VaAndCob/ESP32-OBD2-Gauge/hardware/12-5v micro usb.jpg

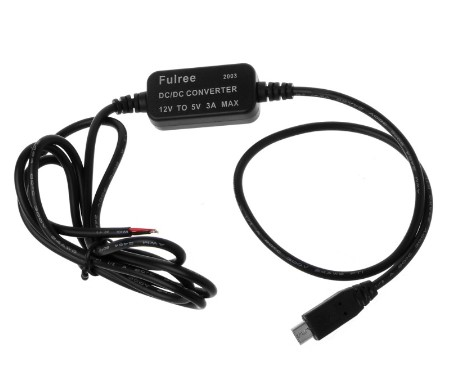
hardware/12-5v micro usb.jpg
