VaAndCob/ESP32-OBD2-Gauge/hardware/ELM327_bluetooth.png

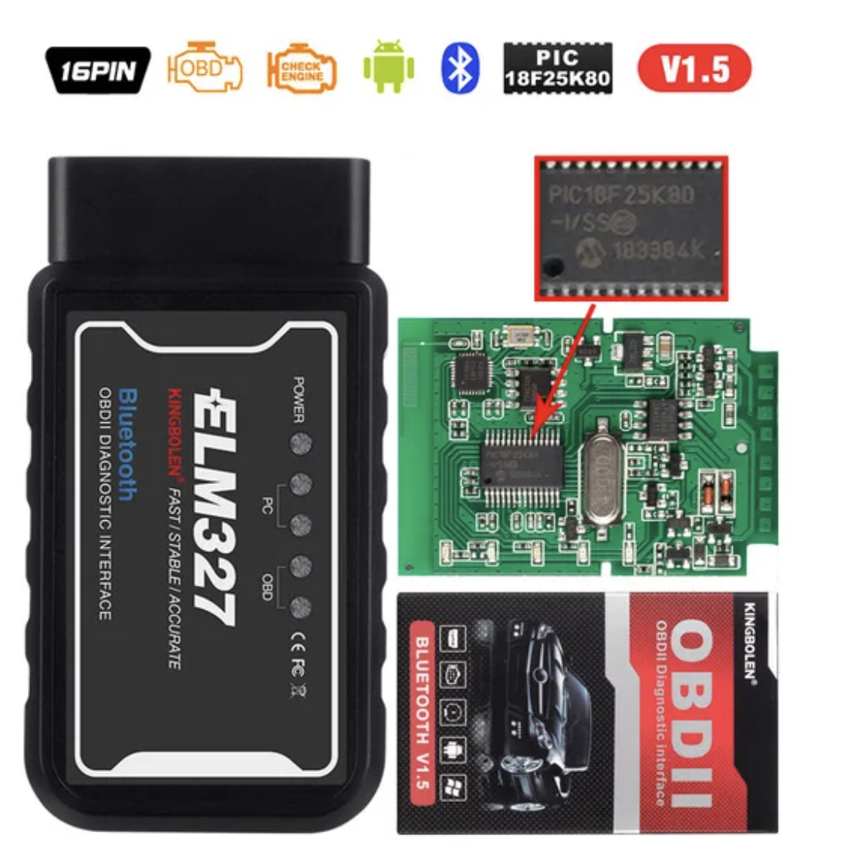
hardware/ELM327_bluetooth.png
