VaAndCob/ESP32-OBD2-Gauge/hardware/ESP32-2432S028-LCM001.jpeg

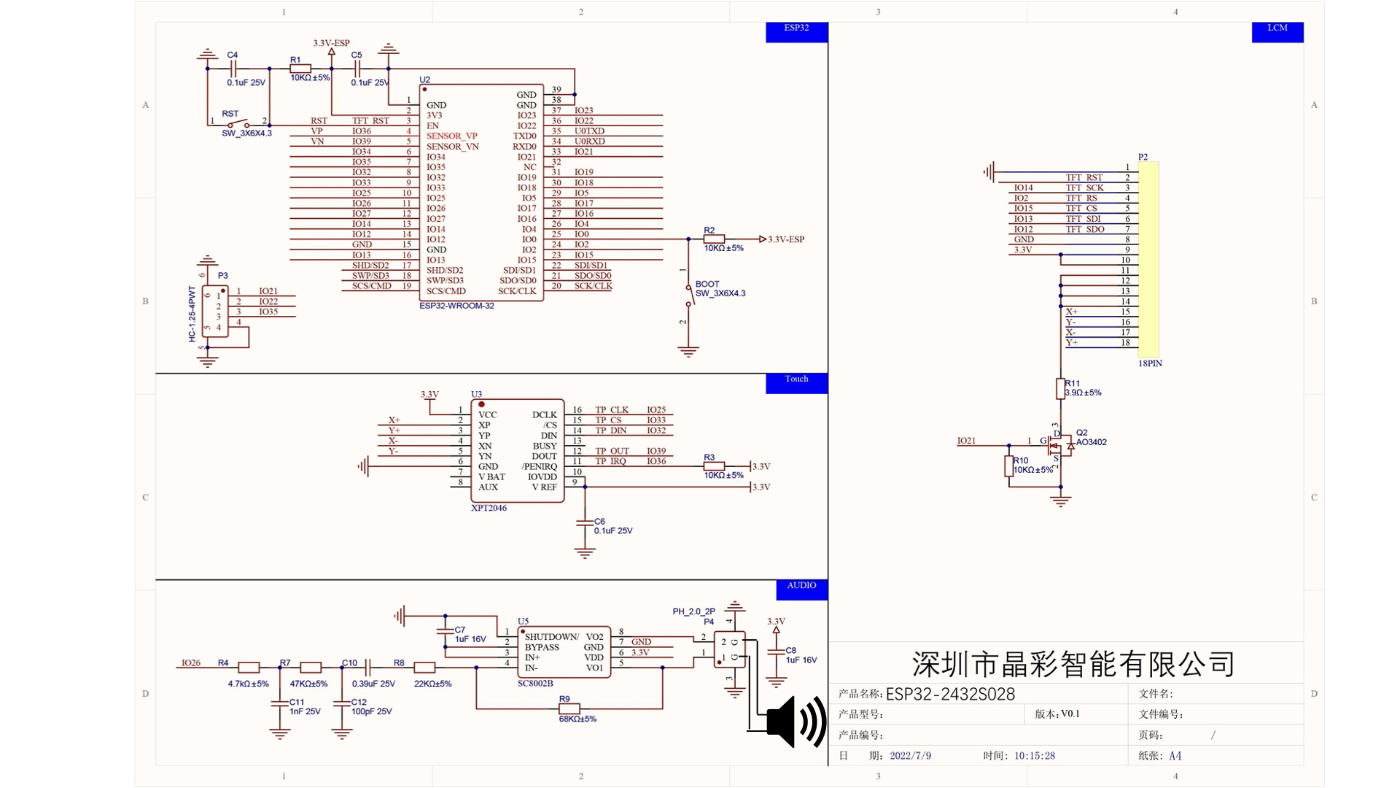
hardware/ESP32-2432S028-LCM001.jpeg
