VaAndCob/ESP32-OBD2-Gauge/picture/cover.jpg

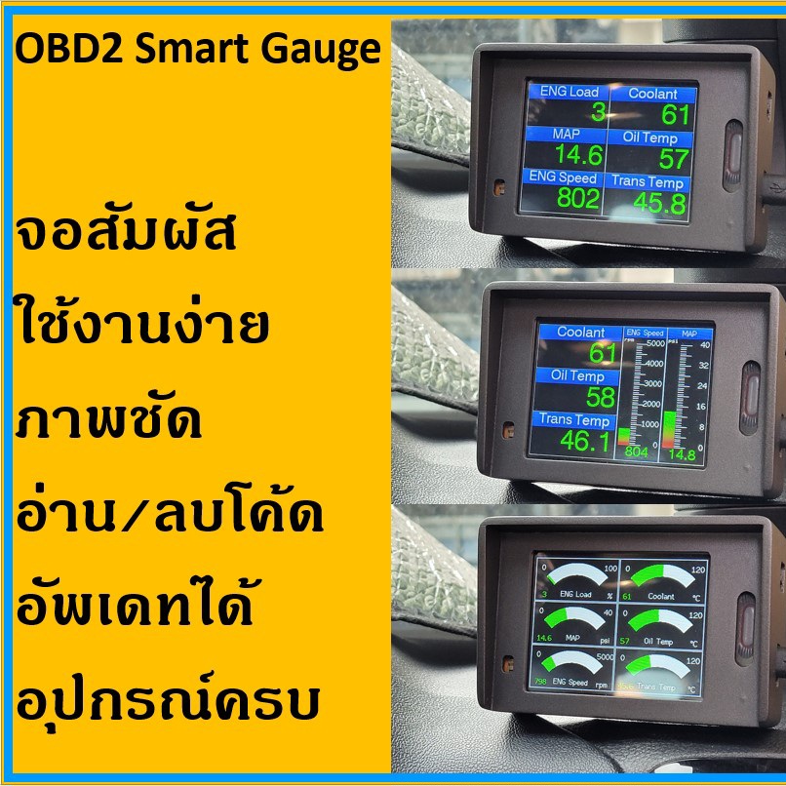
picture/cover.jpg
