VaAndCob/ESP32-OBD2-Gauge/picture/fullpart.jpg

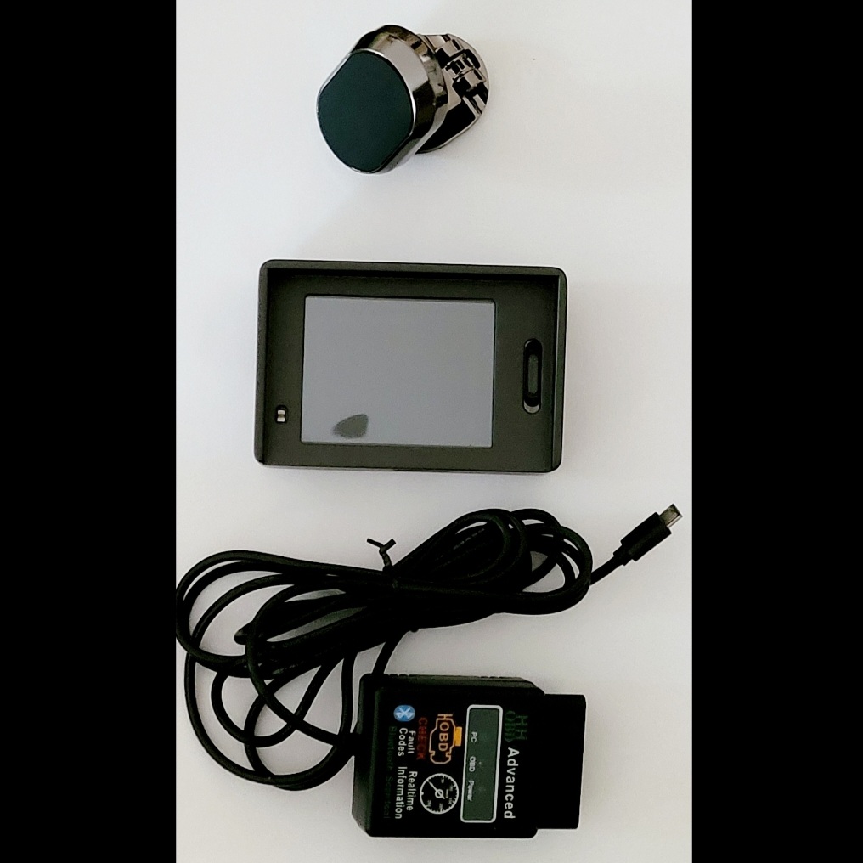
picture/fullpart.jpg
