VaAndCob/ESP32-OBD2-Gauge/picture/gauge.jpg

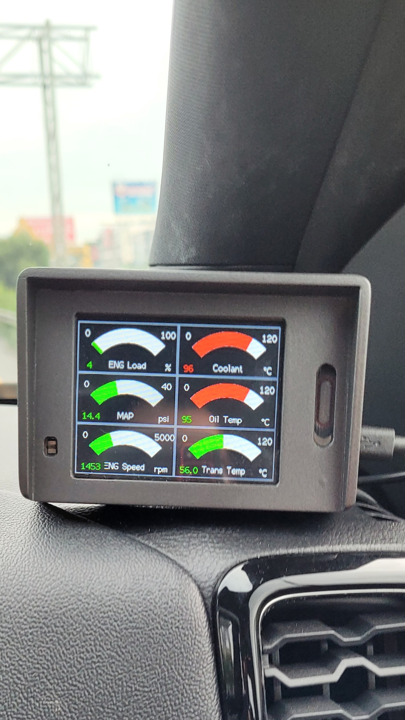
picture/gauge.jpg
