VaAndCob/ESP32-OBD2-Gauge/SDCard/mypic.jpg

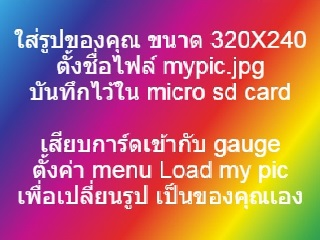
SDCard/mypic.jpg
