VaAndCob/ESP32-OBD2-Gauge/sketch/VaAndCobOBD2Gauge/firmware/offset.png

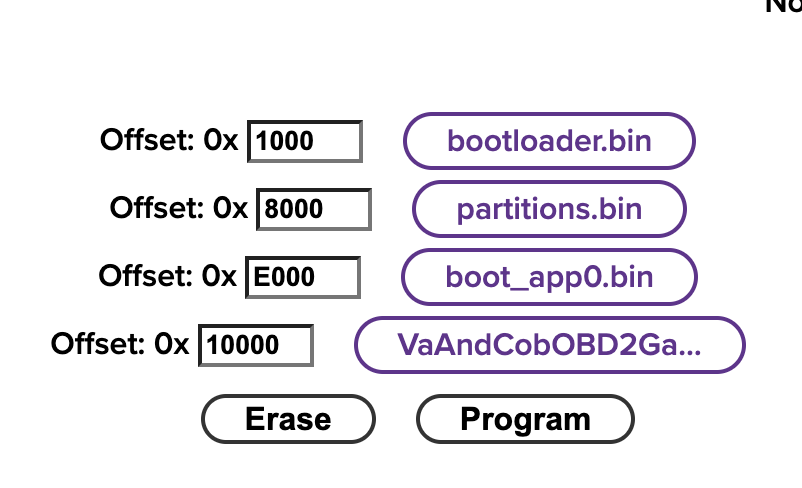
sketch/VaAndCobOBD2Gauge/firmware/offset.png
