VaAndCob/ESP32-OBD2-Gauge/sketch/arduinoSetup.png

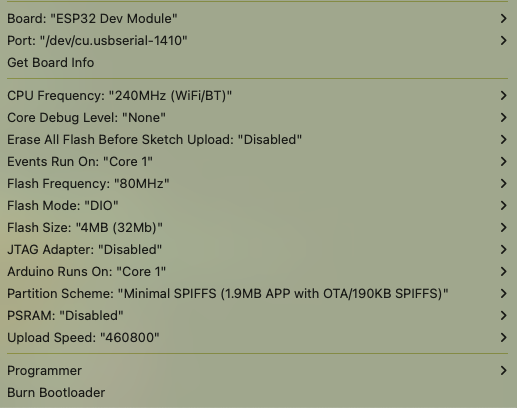
sketch/arduinoSetup.png
