VaAndCob/ESP32-OBD2-Gauge/sketch/VaAndCobOBD2Gauge/firmware_update.h

//Firmware updater library
#include <esp_ota_ops.h>//ota partition boot option
#include <Update.h>  // main updater
#include <FS.h>      // File System
#include <SD.h>      // SD Card ESP32
#include <SPIFFS.h>  //safe file

//Wifi updater
#include <WiFi.h>   //wifi
#include <WebServer.h>

const char* ssid = "Va&Cob OBD2 Gauge";
const char* password = "12345678";//default password
IPAddress local_IP(192, 168, 4,1);
IPAddress gateway(192, 168, 4, 1);
IPAddress subnet(255, 255, 255, 0);
WebServer server(80);

#define firmware_filename "/VaAndCobOBD2Gauge.bin"//firmware file 


/*------------ SOUND EFFECT ----------*/
 void beepbeep() { //2 shot beep
  ledcWriteTone(buzzerChannel,2000);
  delay(50);
  ledcWriteTone(buzzerChannel,0);
  delay(50);
  ledcWriteTone(buzzerChannel,2000);
  delay(50);
  ledcWriteTone(buzzerChannel,0);
 }              
 void beep() { 
  ledcWriteTone(buzzerChannel,2000);
  delay(500);
  ledcWriteTone(buzzerChannel,0);
 }  
 void clickSound() {
  ledcWriteTone(buzzerChannel,5000);
  delay(5);
  ledcWriteTone(buzzerChannel,0);
 } 
 /*-----------------------------*/
//html update file
static const char uploadIndex[] PROGMEM =
R"(
<!DOCTYPE html>
<head>
<meta name='viewport' content='width=device-width'/>
</head>
<body>
<img src="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"width="100%">
<h3 style='color:blue;'>Please choose file 'vaandcobobd2gauge.bin'</h3>
<form method='POST' action='#' enctype='multipart/form-data' id='upload_form'>
<input type='file' name='update' accept=".bin" id='file1' onchange='uploadFile()'>
</form>
<p style='align:center'>
<progress id='progressBar' value='0' max='100' style='width:100%'></progress>
<div id='status' style='text-align:center';>0%</div>
</p>
<script>
function _(el) {
  return document.getElementById(el);
}
function uploadFile() {
  let file = _('file1').files[0];
  // alert(file.name+' | '+file.size+' | '+file.type);
  let req = new XMLHttpRequest();
  let formdata = new FormData();
  formdata.append('file1', file);
   req.upload.addEventListener('progress', progressHandler, false);
  req.addEventListener('load', completeHandler, false);
  req.addEventListener('error', errorHandler, false);
  req.addEventListener('abort', abortHandler, false);
  req.open('POST', '/update'); 
  req.send(formdata);
}
function progressHandler(event) {
  var percent = (event.loaded / event.total) * 100;
  _('progressBar').value = Math.round(percent);
  _('status').innerHTML = Math.round(percent) + '%';
}
function completeHandler(event) {
  _('status').innerHTML = 'Restarting...';
}
function errorHandler(event) {
  _('status').innerHTML = 'Upload Failed';
}
function abortHandler(event) {
  _('status').innerHTML = 'Upload Aborted';
}
</script>
</body>
</html>
)";
/*----- OTA Web Server ------*/
void  StartOTAserver() {
  //open upload page  http://192.168.4.1
  server.on("/", HTTP_GET, []() {
    Serial.println(F("Request upload firmware..."));
    server.sendHeader("Connection", "close");
    server.send(200, "text/html", uploadIndex);
  });

  //handling uploading firmware file http://192.168.4.1/update
  server.on("/update", HTTP_POST, []() {
    server.sendHeader("Connection", "close");
    server.send(200, "text/plain", (Update.hasError()) ? "FAIL" : "OK");
    if (Update.hasError()) {//error 
      tft.setTextColor(TFT_WHITE,TFT_RED);
      tft.drawCentreString("Error: bad firmware file!",159,170,4); 
      beep();
    } 
    else {
      esp_ota_mark_app_valid_cancel_rollback();//prevent from boot old firmware
      delay(3000);
      ESP.restart();//successful upload restart esp
    }  
  }, []() {
    
    HTTPUpload& upload = server.upload();
    if (upload.status == UPLOAD_FILE_START) {
      beepbeep();
      Serial.printf("Firmware: %s\n", upload.filename.c_str());
      tft.setTextColor(TFT_BLACK,TFT_GREEN);
      tft.drawCentreString("Updating... please wait",159,170,4); 
      if (!Update.begin(UPDATE_SIZE_UNKNOWN)) { //start with max available size
        Update.printError(Serial);        
      }
    } else if (upload.status == UPLOAD_FILE_WRITE) {
      // flashing firmware to ESP
      if (Update.write(upload.buf, upload.currentSize) != upload.currentSize) {
        Update.printError(Serial);
      }
    } else if (upload.status == UPLOAD_FILE_END) {
      if (Update.end(true)) { //true to set the size to the current progress
        Serial.printf("Update Successful... Restart");
        tft.setTextColor(TFT_BLACK,TFT_GREEN);
        tft.drawCentreString("Update Successful... Restart",159,170,4); 
        beepbeep();

      } else {
        Update.printError(Serial);  
      }
    }
  });
  server.begin();
}//startOTAserver
/*-------------- WiFi Updater----------------*/
void updateFirmwareWIFI() {  
  WiFi.mode(WIFI_AP);//set wifi mode soft access point
  String pwd = String(random(99999999));//random new password at least 8 digit long to get it work
  for (uint8_t i=pwd.length();i<8;i++) {
    pwd = "0"+pwd;//add 0 prefix to set 8 char length password
  }
  password = pwd.c_str();
  WiFi.softAP(ssid, password);//start ACCESS Point
  if (!WiFi.softAPConfig(local_IP, gateway, subnet)) {//error start soft AP
    Serial.println(F("STA Failed to configure"));
    tft.setTextColor(TFT_WHITE,TFT_RED);
    tft.drawCentreString("Failed to start WiFi!",159,120,4); 
    beep();
    delay(3000); 
  } else {//softAP config OK
    StartOTAserver();//start server
  //show WiFi softAP information
    tft.fillRect(0,30,320,239,TFT_BLACK);
    tft.setTextColor(TFT_CYAN,TFT_BLACK);
    tft.drawCentreString("> Connect to gauge Wi-Fi <",159,40,4); 
    tft.setTextColor(TFT_WHITE,TFT_BLACK); 
    String txt = "SSID: "+String(ssid);
    Serial.println(txt);
    tft.drawString(txt,0,80,4);
    txt = "Password: "+String(password);
    Serial.println(txt);
    tft.drawString(txt,0,110,4);
    txt = "IP Address: "+ WiFi.softAPIP().toString();
    Serial.println(txt);
    tft.drawString(txt,0,140,4);  
    tft.setTextColor(TFT_BLACK,TFT_WHITE);
    tft.drawCentreString("[- Press button to exit -]",159,215,4);  
    while (digitalRead(SELECTOR_PIN) == HIGH) {//wait for button press to exit       
      autoDim();
      checkCPUTemp(); 
      server.handleClient();//update server handle      
      delay(300);//delay button press
    } //exit wifi update      
    clickSound();   
    server.stop();
    WiFi.mode(WIFI_MODE_STA);
    WiFi.softAPdisconnect();//turn off WiFi
  }//else WiFi.softapconfig
} //updateFirmwareWiFI
/*----------- SD Card Updater --------------*/
// perform the actual update from a given stream
void performUpdate(Stream &updateSource, size_t updateSize) {
  if (Update.begin(updateSize, U_FLASH, LED_RED_PIN, LOW)) { 
      //add progressbar
      tft.fillRoundRect(50,61, 218, 28, 14, TFT_LIGHTGREY);
      tft.fillRect(59,67,200,16,TFT_BLACK);//0% progress bar
      //update progress
      Serial.print(F("Progress: "));
      //progress callback
     Update.onProgress([&](size_t written, size_t total) {
      uint8_t progress = written * 100 / total;
      tft.fillRectHGradient(59,67,progress*2,16,TFT_RED,TFT_GREEN);//progressbar 
      if (progress%10 == 0) Serial.print(F("*"));
      ledcWriteTone(buzzerChannel,random(4000)+8000);//acceleraet sound effect
    }); 

    //write firmware from SDCard here
      size_t written = Update.writeStream(updateSource);
      Serial.printf("%d bytes written",written);

     if (Update.end()) {//updaet is done
         if (Update.isFinished()) {
            Serial.println(F("Update Successful... Restart"));
            tft.setTextColor(TFT_BLACK,TFT_GREEN);
            tft.drawCentreString("Update Successful... Restart",159,120,4);  
            beepbeep();
            esp_ota_mark_app_valid_cancel_rollback();//prevent from boot old firmware
            delay(1000);
            ESP.restart();//restart
         }
         else {
            Serial.println(F("Error! Update not finished"));
            tft.setTextColor(TFT_WHITE,TFT_RED);
            tft.drawCentreString("Error! Update not finished",159,120,4); 
         }
      } else {//update stop during updating
         Serial.println("Error Occurred. Error #: " + String(Update.getError()));
      }

   }//if update.begin
   else
   {
      Serial.println(F("Not enough space to load firmware"));
      tft.setTextColor(TFT_WHITE,TFT_RED);
      tft.drawCentreString("Not enough space to upload!",159,120,4); 
   }
}
/*------------------*/
// check given FS for valid update.bin and perform update if available
void updateFromFS(fs::FS &fs) {
   Serial.println(F("Loading firmware..."));
   tft.setTextColor(TFT_WHITE,TFT_BLUE);
   tft.drawCentreString("Loading firmware...",159,120,4);
   File updateBin = fs.open(firmware_filename);
   if (updateBin) {
 
      if(updateBin.isDirectory()){
         Serial.println(F("\"VaandCobOBD2Gauge.bin\" is not a file"));
         tft.setTextColor(TFT_WHITE,TFT_RED);
         tft.drawCentreString("\"VaandCobOBD2Gauge.bin\" is not a file",159,120,4);
         updateBin.close();
         return;
      }
    
      size_t updateSize = updateBin.size();

      if (updateSize > 0) {
         Serial.println(F("Updating... please wait"));
         tft.setTextColor(TFT_WHITE,TFT_BLUE);
         tft.drawCentreString("Updating... please wait",159,120,4);
         performUpdate(updateBin, updateSize);
      }
      else {
         Serial.println(F("Error! file is empty"));
         tft.setTextColor(TFT_WHITE,TFT_RED);
         tft.drawCentreString("Error! file is empty",159,120,4);               
      }
      updateBin.close();
      // whe finished remove the binary from sd card to indicate end of the process
      //fs.remove(firmware_filename);  
   
   } else {
      Serial.println(F("Firmware not found!"));
      tft.pushImage(130,44,60,60,nofile);//show fileicon
      tft.setTextColor(TFT_WHITE,TFT_RED);
      tft.drawCentreString("Firmware not found!",159,120,4);
   }

}
/*------------------*/
void updateFirmwareSD() {
  tft.fillRect(0,30,320,239,TFT_BLACK);
  tft.setTextColor(TFT_BLACK,TFT_WHITE);
  tft.drawCentreString("[- Press button to exit -]",159,215,4);  
   if(!SD.begin()) {//sdcard not attach
    Serial.println(F("Micro SD Card not mounted!"));
    tft.pushImage(129,44,60,60,sdcard);//show sdcard icon
    tft.setTextColor(TFT_WHITE,TFT_RED);
    tft.drawCentreString("Please insert Micro SD Card",159,120,4);
  } else {//sd card attached
    Serial.println(F("Micro SD Card..OK")); 
    uint8_t cardType = SD.cardType(); 
    if (cardType == CARD_NONE) {//bad card
      Serial.println(F("Micro SD Card Error!"));
      tft.setTextColor(TFT_WHITE,TFT_RED);
      tft.drawCentreString("Micro SD Card Error!",159,120,4);
     } else {//good sd card attached
      updateFromFS(SD);//update firmware from sd card
       
     }//else  
  }//else
   SD.end();
   beep();
}//updatefirmware
/*----------------*/
