VaAndCob/ESP32-OBD2-Gauge/sketch/VaAndCobOBD2Gauge/music.h

 static const uint8_t song[18316] PROGMEM = {
  0x56, 0x67, 0x6D, 0x20, 0x88, 0x47, 0x00, 0x00, 0x61, 0x01, 0x00, 0x00, 0x00, 0x00, 0x00, 0x00, 0x00, 0x00, 0x00, 0x00, 0x8E, 0x46, 0x00, 0x00, 0x8F, 0xEE, 0x19, 0x00, 0xFB, 0x00, 0x00, 0x00, 0x37, 0xCC, 0x19, 0x00, 0x00, 0x00, 0x00, 0x00, 0x00, 0x00, 0x00, 0x00, 0x00, 0x00, 0x00, 0x00, 0x00, 0x00, 0x00, 0x00, 0x8C, 0x00, 0x00, 0x00, 0x00, 0x00, 0x00, 0x00, 0x00, 0x00, 0x00, 0x00, 0x00, 0x00, 0x00, 0x00, 0x00, 0x00, 0x00, 0x00, 0x00, 0x00, 0x00, 0x00, 0x00, 0x00, 0x00, 0x00, 0x00, 0x00, 0x00, 0x00, 0x00, 0x00, 0x00, 0x00, 0x00, 0x00, 0x00, 0x00, 0x00, 0x00, 0x00, 0x00, 0x00, 0x00, 0x00, 0x00, 0x00, 0x00, 0x00, 0x00, 0x00, 0x00, 0x00, 0x00, 0x00, 0x00, 0x00, 0x00, 0x00, 0x00, 0x00, 0x00, 0x00, 0x00, 0x00, 0x00, 0x00, 0x00, 0x00, 0x00, 0x00, 0x00, 0x00, 0x00, 0x00, 0x00, 0x00, 0x00, 0x4C, 0x4F, 0x1B, 0x00, 0x00, 0x00, 0x00, 0x00, 0x00, 0x00, 0x00, 0x00, 0x00, 0x00, 0x00, 0x00, 0x00, 0x00, 
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
  0x04, 0xB9, 0x70, 0xB4, 0x06, 0x34, 0xB4, 0x07, 0x00, 0x61, 0xCE, 0x02, 0xB4, 0x00, 0xBB, 0x62, 0x75, 0xB4, 0x04, 0xB7, 0x61, 0xDC, 0x02, 0xB4, 0x00, 0xB9, 0x61, 0xDC, 0x02, 0xB4, 0x04, 0xB6, 0x70, 0xB4, 0x06, 0x35, 0x61, 0xDE, 0x02, 0xB4, 0x00, 0xB7, 0x62, 0x76, 0xB4, 0x00, 0xBF, 0xB4, 0x02, 0x54, 0x70, 0xB4, 0x03, 0x00, 0x70, 0xB4, 0x04, 0xB5, 0x61, 0xB4, 0x05, 0xB4, 0x00, 0xBD, 0x71, 0xB4, 0x04, 0xB4, 0x62, 0x73, 0xB4, 0x04, 0xB9, 0x70, 0xB4, 0x06, 0x46, 0x70, 0xB4, 0x07, 0x00, 0x61, 0xCD, 0x02, 0xB4, 0x00, 0xBB, 0x62, 0x75, 0xB4, 0x04, 0xB7, 0x61, 0xDC, 0x02, 0xB4, 0x00, 0xB9, 0x61, 0xDC, 0x02, 0xB4, 0x04, 0xB6, 0x70, 0xB4, 0x06, 0x47, 0x62, 0xB4, 0x00, 0xB7, 0x62, 0x75, 0xB4, 0x00, 0xBF, 0x70, 0xB4, 0x02, 0x5E, 0xB4, 0x03, 0x00, 0x70, 0xB4, 0x04, 0xB5, 0x61, 0xB4, 0x05, 0xB4, 0x00, 0xBD, 0x71, 0xB4, 0x04, 0xB4, 0x62, 0x72, 0xB4, 0x04, 0xB9, 0x70, 0xB4, 0x06, 0x54, 0x70, 0xB4, 0x07, 
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
};
